khill25/Dreamdrive64/sw/dreamdrive64/sram.h

/**
 * SPDX-License-Identifier: BSD-2-Clause
 *
 * Copyright (c) 2022 Konrad Beckmann
 */

#pragma once

#include <stdint.h>

#define SRAM_256KBIT_SIZE         0x00008000
#define SRAM_768KBIT_SIZE         0x00018000
#define SRAM_1MBIT_SIZE           0x00020000

extern uint16_t *sram;
